augussong/VFD-Clock/Reference/IV-11引脚定义-英文版.jpg

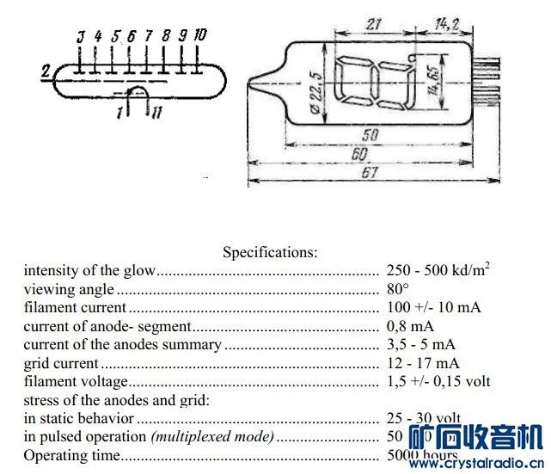
Reference/IV-11引脚定义-英文版.jpg
