augussong/VFD-Clock/Project/Software/VFD-Clock/Bsp/i2c.c

/**
  ******************************************************************************
  * @file    bsp_i2c_ee.c
  * @author  armfly 
  * @version V1.0
  * @date    2013-xx-xx
  * @brief   用gpio模拟i2c总线, 适用于STM32系列CPU。该模块不包括应用层命令帧，仅包括I2C总线基本操作函数。
  ******************************************************************************
  * @attention
  *
  * 实验平台:野火 ISO-MINI STM32 开发板 
  * 论坛    :http://www.chuxue123.com
  * 淘宝    :http://firestm32.taobao.com
  *
  ******************************************************************************
  */ 

/*
	应用说明：
	在访问I2C设备前，请先调用 i2c_CheckDevice() 检测I2C设备是否正常，该函数会配置GPIO
*/

#include "stm32f10x.h"
#include "i2c.h"

/*
*********************************************************************************************************
*	函 数 名: i2c_Delay
*	功能说明: I2C总线位延迟，最快400KHz
*	形    参：无
*	返 回 值: 无
*********************************************************************************************************
*/
void i2c_Delay(void)
{
	uint8_t i;

	/*　
	 	下面的时间是通过安富莱AX-Pro逻辑分析仪测试得到的。
		CPU主频72MHz时，在内部Flash运行, MDK工程不优化
		循环次数为10时，SCL频率 = 205KHz 
		循环次数为7时，SCL频率 = 347KHz， SCL高电平时间1.5us，SCL低电平时间2.87us 
	 	循环次数为5时，SCL频率 = 421KHz， SCL高电平时间1.25us，SCL低电平时间2.375us 
        
    IAR工程编译效率高，不能设置为7
	*/
	for (i = 0; i < 10; i++);
}

/*
*********************************************************************************************************
*	函 数 名: i2c_Start
*	功能说明: CPU发起I2C总线启动信号
*	形    参：无
*	返 回 值: 无
*********************************************************************************************************
*/
void i2c_Start(void)
{
	/* 当SCL高电平时，SDA出现一个下跳沿表示I2C总线启动信号 */
	I2C_SDA_1();
	I2C_SCL_1();
	i2c_Delay();
	I2C_SDA_0();
	i2c_Delay();
	I2C_SCL_0();
	i2c_Delay();
}

/*
*********************************************************************************************************
*	函 数 名: i2c_Start
*	功能说明: CPU发起I2C总线停止信号
*	形    参：无
*	返 回 值: 无
*********************************************************************************************************
*/
void i2c_Stop(void)
{
	/* 当SCL高电平时，SDA出现一个上跳沿表示I2C总线停止信号 */
	I2C_SDA_0();
	I2C_SCL_1();
	i2c_Delay();
	I2C_SDA_1();
	i2c_Delay();
}

/*
*********************************************************************************************************
*	函 数 名: i2c_SendByte
*	功能说明: CPU向I2C总线设备发送8bit数据
*	形    参：_ucByte ： 等待发送的字节
*	返 回 值: 无
*********************************************************************************************************
*/
void i2c_SendByte(uint8_t _ucByte)
{
	uint8_t i;

	/* 先发送字节的高位bit7 */
	for (i = 0; i < 8; i++)
	{		
		if (_ucByte & 0x80)
		{
			I2C_SDA_1();
		}
		else
		{
			I2C_SDA_0();
		}
		i2c_Delay();
		I2C_SCL_1();
		i2c_Delay();	
		I2C_SCL_0();
		if (i == 7)
		{
			 I2C_SDA_1(); // 释放总线
		}
		_ucByte <<= 1;	/* 左移一个bit */
		i2c_Delay();
	}
	i2c_Delay();
}

/*
*********************************************************************************************************
*	函 数 名: i2c_ReadByte
*	功能说明: CPU从I2C总线设备读取8bit数据
*	形    参：无
*	返 回 值: 读到的数据
*********************************************************************************************************
*/
uint8_t i2c_ReadByte(void)
{
	uint8_t i;
	uint8_t value;

	/* 读到第1个bit为数据的bit7 */
	value = 0;
	for (i = 0; i < 8; i++)
	{
		value <<= 1;
		I2C_SCL_1();
		i2c_Delay();
		if (I2C_SDA_READ())
		{
			value++;
		}
		I2C_SCL_0();
		i2c_Delay();
	}
	i2c_Delay();
	return value;
}

/*
*********************************************************************************************************
*	函 数 名: i2c_WaitAck
*	功能说明: CPU产生一个时钟，并读取器件的ACK应答信号
*	形    参：无
*	返 回 值: 返回0表示正确应答，1表示无器件响应
*********************************************************************************************************
*/
uint8_t i2c_WaitAck(void)
{
	uint8_t re;

	I2C_SDA_1();	/* CPU释放SDA总线 */
	i2c_Delay();
	I2C_SCL_1();	/* CPU驱动SCL = 1, 此时器件会返回ACK应答 */
	i2c_Delay();
	if (I2C_SDA_READ())	/* CPU读取SDA口线状态 */
	{
		re = 1;
	}
	else
	{
		re = 0;
	}
	I2C_SCL_0();
	i2c_Delay();
	return re;
}

/*
*********************************************************************************************************
*	函 数 名: i2c_Ack
*	功能说明: CPU产生一个ACK信号
*	形    参：无
*	返 回 值: 无
*********************************************************************************************************
*/
void i2c_Ack(void)
{
	I2C_SDA_0();	/* CPU驱动SDA = 0 */
	i2c_Delay();
	I2C_SCL_1();	/* CPU产生1个时钟 */
	i2c_Delay();
	I2C_SCL_0();
	i2c_Delay();
	I2C_SDA_1();	/* CPU释放SDA总线 */
	i2c_Delay();
}

/*
*********************************************************************************************************
*	函 数 名: i2c_NAck
*	功能说明: CPU产生1个NACK信号
*	形    参：无
*	返 回 值: 无
*********************************************************************************************************
*/
void i2c_NAck(void)
{
	I2C_SDA_1();	/* CPU驱动SDA = 1 */
	i2c_Delay();
	I2C_SCL_1();	/* CPU产生1个时钟 */
	i2c_Delay();
	I2C_SCL_0();
	i2c_Delay();	
}

/*
*********************************************************************************************************
*	函 数 名: IIC_WriteBytes
*	功能说明: 向指定地址写入若干数据，采用页写操作提高写入效率
*	形    参：_usAddress : 起始地址（寄存器地址）
*			 _usSize : 数据长度，单位为字节
*			 _pWriteBuf : 存放要写的数据的缓冲区指针
*			 _usDevAddr : 设备地址
*	返 回 值: 0 表示失败，1表示成功
*********************************************************************************************************
*/
uint8_t IIC_WriteBytes(uint8_t *_pWriteBuf, uint16_t _usAddress, uint16_t _usSize, uint16_t _usDevAddr)
{
	uint16_t i,m;
	uint16_t usAddr;
	

	usAddr = _usAddress;	
	for (i = 0; i < _usSize; i++)
	{
		/* 当发送第1个字节或是页面首地址时，需要重新发起启动信号和地址 */
		if (i == 0)
		{
			/*　第０步：发停止信号，启动内部写操作　*/
			i2c_Stop();
			
			/* 通过检查器件应答的方式，判断内部写操作是否完成, 一般小于 10ms 			
				CLK频率为200KHz时，查询次数为30次左右
			*/
			for (m = 0; m < 100; m++)
			{				
				/* 第1步：发起I2C总线启动信号 */
				i2c_Start();
				
				/* 第2步：发起控制字节，高7bit是地址，bit0是读写控制位，0表示写，1表示读 */
				i2c_SendByte(_usDevAddr | I2C_WR);	/* 此处是写指令 */
				
				/* 第3步：发送一个时钟，判断器件是否正确应答 */
				if (i2c_WaitAck() == 0)
				{
					break;
				}
			}
			if (m  == 1000)
			{
				goto cmd_fail;	/* 写超时 */
			}
		
			/* 第4步：发送字节地址*/
			i2c_SendByte((uint8_t)usAddr);
			
			/* 第5步：发送ACK */
			if (i2c_WaitAck() != 0)
			{
				goto cmd_fail;	/* EEPROM器件无应答 */
			}
		}
	
		/* 第6步：开始写入数据 */
		i2c_SendByte(_pWriteBuf[i]);
	
		/* 第7步：发送ACK */
		if (i2c_WaitAck() != 0)
		{
			goto cmd_fail;	/* EEPROM器件无应答 */
		}

		usAddr++;	/* 地址增1 */		
	}
	
	/* 命令执行成功，发送I2C总线停止信号 */
	i2c_Stop();
	return 1;

cmd_fail: /* 命令执行失败后，切记发送停止信号，避免影响I2C总线上其他设备 */
	/* 发送I2C总线停止信号 */
	i2c_Stop();
	return 0;
}

/*
*********************************************************************************************************
*	函 数 名: IIC_ReadBytes
*	功能说明: 从指定地址处开始读取若干数据
*	形    参：_usAddress : 起始地址（寄存器地址）
*			 _usSize : 数据长度，单位为字节
*			 _pReadBuf : 存放读到的数据的缓冲区指针
*			 _usDevAddr : 设备地址
*	返 回 值: 0 表示失败，1表示成功
*********************************************************************************************************
*/
uint8_t IIC_ReadBytes(uint8_t *_pReadBuf, uint16_t _usAddress, uint16_t _usSize, uint16_t _usDevAddr)
{
	uint16_t i;
	
	/* 第1步：发起I2C总线启动信号 */
	i2c_Start();
	
	/* 第2步：发起控制字节，高7bit是地址，bit0是读写控制位，0表示写，1表示读 */
	i2c_SendByte(_usDevAddr | I2C_WR);	/* 此处是写指令 */
	
	/* 第3步：发送ACK */
	if (i2c_WaitAck() != 0)
	{
		goto cmd_fail;	/* 器件无应答 */
	}

	/* 第4步：发送字节地址*/
	i2c_SendByte((uint8_t)_usAddress);
	
	/* 第5步：发送ACK */
	if (i2c_WaitAck() != 0)
	{
		goto cmd_fail;	/*器件无应答 */
	}
	
	/* 第6步：重新启动I2C总线。前面的代码的目的向EEPROM传送地址，下面开始读取数据 */
	i2c_Start();
	
	/* 第7步：发起控制字节，高7bit是地址，bit0是读写控制位，0表示写，1表示读 */
	i2c_SendByte(_usDevAddr | I2C_RD);	/* 此处是读指令 */
	
	/* 第8步：发送ACK */
	if (i2c_WaitAck() != 0)
	{
		goto cmd_fail;	/* 器件无应答 */
	}	
	
	/* 第9步：循环读取数据 */
	for (i = 0; i < _usSize; i++)
	{
		_pReadBuf[i] = i2c_ReadByte();	/* 读1个字节 */
		
		/* 每读完1个字节后，需要发送Ack， 最后一个字节不需要Ack，发Nack */
		if (i != _usSize - 1)
		{
			i2c_Ack();	/* 中间字节读完后，CPU产生ACK信号(驱动SDA = 0) */
		}
		else
		{
			i2c_NAck();	/* 最后1个字节读完后，CPU产生NACK信号(驱动SDA = 1) */
		}
	}
	/* 发送I2C总线停止信号 */
	i2c_Stop();
	return 1;	/* 执行成功 */

cmd_fail: /* 命令执行失败后，切记发送停止信号，避免影响I2C总线上其他设备 */
	/* 发送I2C总线停止信号 */
	i2c_Stop();
	return 0;
}

/*
*********************************************************************************************************
*	函 数 名: i2c_CfgGpio
*	功能说明: 配置I2C总线的GPIO，采用模拟IO的方式实现
*	形    参：无
*	返 回 值: 无
*********************************************************************************************************
*/
void i2c_CfgGpio(void)
{
	GPIO_InitTypeDef GPIO_InitStructure;

	RCC_APB2PeriphClockCmd(RCC_I2C_PORT, ENABLE);	/* 打开GPIO时钟 */

	GPIO_InitStructure.GPIO_Pin = I2C_SCL_PIN | I2C_SDA_PIN;
	GPIO_InitStructure.GPIO_Speed = GPIO_Speed_50MHz;
	GPIO_InitStructure.GPIO_Mode = GPIO_Mode_Out_OD;  	/* 开漏输出 */
	GPIO_Init(GPIO_PORT_I2C, &GPIO_InitStructure);

	/* 给一个停止信号, 复位I2C总线上的所有设备到待机模式 */
	i2c_Stop();
}

/*
*********************************************************************************************************
*	函 数 名: i2c_CheckDevice
*	功能说明: 检测I2C总线设备，CPU向发送设备地址，然后读取设备应答来判断该设备是否存在
*	形    参：_Address：设备的I2C总线地址
*	返 回 值: 返回值 0 表示正确， 返回1表示未探测到
*********************************************************************************************************
*/
uint8_t i2c_CheckDevice(uint8_t _Address)
{
	uint8_t ucAck;

	i2c_CfgGpio();		/* 配置GPIO */

	
	i2c_Start();		/* 发送启动信号 */

	/* 发送设备地址+读写控制bit（0 = w， 1 = r) bit7 先传 */
	i2c_SendByte(_Address | I2C_WR);
	ucAck = i2c_WaitAck();	/* 检测设备的ACK应答 */

	i2c_Stop();			/* 发送停止信号 */

	return ucAck;
}
