augussong/VFD-Clock/Project/Software/VFD-Clock/User_USB/hw_config.c

/******************** (C) COPYRIGHT 2009 STMicroelectronics ********************
* File Name          : hw_config.c
* Author             : MCD Application Team
* Version            : V3.0.1
* Date               : 04/27/2009
* Description        : Hardware Configuration & Setup
********************************************************************************
* THE PRESENT FIRMWARE WHICH IS FOR GUIDANCE ONLY AIMS AT PROVIDING CUSTOMERS
* WITH CODING INFORMATION REGARDING THEIR PRODUCTS IN ORDER FOR THEM TO SAVE TIME.
* AS A RESULT, STMICROELECTRONICS SHALL NOT BE HELD LIABLE FOR ANY DIRECT,
* INDIRECT OR CONSEQUENTIAL DAMAGES WITH RESPECT TO ANY CLAIMS ARISING FROM THE
* CONTENT OF SUCH FIRMWARE AND/OR THE USE MADE BY CUSTOMERS OF THE CODING
* INFORMATION CONTAINED HEREIN IN CONNECTION WITH THEIR PRODUCTS.
*******************************************************************************/

/* Includes ------------------------------------------------------------------*/
#include "stm32f10x_it.h"
#include "usb_lib.h"
#include "usb_prop.h"
#include "usb_desc.h"
#include "hw_config.h"
#include "platform_config.h"
#include "usb_pwr.h"

/* Private typedef -----------------------------------------------------------*/
/* Private define ------------------------------------------------------------*/
/* Private macro -------------------------------------------------------------*/
/* Private variables ---------------------------------------------------------*/

/* Extern variables ----------------------------------------------------------*/
uint8_t buffer_in[VIRTUAL_COM_PORT_DATA_SIZE];

/* Private function prototypes -----------------------------------------------*/
/* Private functions ---------------------------------------------------------*/
/*******************************************************************************
* Function Name  : Set_System
* Description    : Configures Main system clocks & power
* Input          : None.
* Return         : None.
*******************************************************************************/
void Set_System(void)
{
  GPIO_InitTypeDef GPIO_InitStructure;

  /* Setup the microcontroller system. Initialize the Embedded Flash Interface,  
     initialize the PLL and update the SystemFrequency variable. */
//  SystemInit();

  /* Enable USB_DISCONNECT GPIO clock */
  RCC_APB2PeriphClockCmd(RCC_APB2Periph_GPIO_DISCONNECT, ENABLE);

  /* Configure USB pull-up pin */
  GPIO_InitStructure.GPIO_Pin = USB_DISCONNECT_PIN;
  GPIO_InitStructure.GPIO_Speed = GPIO_Speed_50MHz;
  GPIO_InitStructure.GPIO_Mode = GPIO_Mode_Out_OD;
  GPIO_Init(USB_DISCONNECT, &GPIO_InitStructure);
}

/*******************************************************************************
* Function Name  : USB_PreInit
* Description    : Configures USB clocks, connect pin, and interrupt.
*									 本函数将初始化中用到的本文件的其他函数封装了起来
* Input          : None.
* Return         : None.
*******************************************************************************/
void USB_PreInit(void)
{
	GPIO_InitTypeDef GPIO_InitStructure;
	
	/* Enable USB_DISCONNECT GPIO clock */
  RCC_APB2PeriphClockCmd(RCC_APB2Periph_GPIO_DISCONNECT, ENABLE);

  /* Configure USB pull-up pin */
  GPIO_InitStructure.GPIO_Pin = USB_DISCONNECT_PIN;
  GPIO_InitStructure.GPIO_Speed = GPIO_Speed_50MHz;
  GPIO_InitStructure.GPIO_Mode = USB_GPIO_MODE;
  GPIO_Init(USB_DISCONNECT, &GPIO_InitStructure);
	
	// 初始化USB时钟
	Set_USBClock();
	
	//初始化USB中断（在其他地方处理）
//	USB_Interrupts_Config();
}

/*******************************************************************************
* Function Name  : Set_USBClock
* Description    : Configures USB Clock input (48MHz)
* Input          : None.
* Return         : None.
*******************************************************************************/
void Set_USBClock(void)
{
  /* USBCLK = PLLCLK / 1.5 */
  RCC_USBCLKConfig(RCC_USBCLKSource_PLLCLK_1Div5);
  /* Enable USB clock */
  RCC_APB1PeriphClockCmd(RCC_APB1Periph_USB, ENABLE);
}

/*******************************************************************************
* Function Name  : Enter_LowPowerMode
* Description    : Power-off system clocks and power while entering suspend mode
* Input          : None.
* Return         : None.
*******************************************************************************/
void Enter_LowPowerMode(void)
{
  /* Set the device state to suspend */
  bDeviceState = SUSPENDED;
}

/*******************************************************************************
* Function Name  : Leave_LowPowerMode
* Description    : Restores system clocks and power while exiting suspend mode
* Input          : None.
* Return         : None.
*******************************************************************************/
void Leave_LowPowerMode(void)
{
  DEVICE_INFO *pInfo = &Device_Info;

  /* Set the device state to the correct state */
  if (pInfo->Current_Configuration != 0)
  {
    /* Device configured */
    bDeviceState = CONFIGURED;
  }
  else
  {
    bDeviceState = ATTACHED;
  }
}

/*******************************************************************************
* Function Name  : USB_Interrupts_Config
* Description    : Configures the USB interrupts
* Input          : None.
* Return         : None.
*******************************************************************************/
void USB_Interrupts_Config(void)
{
  NVIC_InitTypeDef NVIC_InitStructure;

  NVIC_PriorityGroupConfig(NVIC_PriorityGroup_1);

  NVIC_InitStructure.NVIC_IRQChannel = USB_LP_CAN1_RX0_IRQn;
  NVIC_InitStructure.NVIC_IRQChannelPreemptionPriority = 0;
  NVIC_InitStructure.NVIC_IRQChannelSubPriority = 0;
  NVIC_InitStructure.NVIC_IRQChannelCmd = ENABLE;
  NVIC_Init(&NVIC_InitStructure);
}

/*******************************************************************************
* Function Name  : USB_Cable_Config
* Description    : Software Connection/Disconnection of USB Cable
* Input          : None.
* Return         : Status
*******************************************************************************/
void USB_Cable_Config (FunctionalState NewState)
{
  if (NewState != DISABLE)
  {
    CONNECT_CABLE();
  }
  else
  {
    DISCONNECT_CABLE();
  }
}

/*******************************************************************************
* Function Name  : Get_SerialNum.
* Description    : Create the serial number string descriptor.
* Input          : None.
* Output         : None.
* Return         : None.
*******************************************************************************/
void Get_SerialNum(void)
{
  uint32_t Device_Serial0, Device_Serial1, Device_Serial2;

  Device_Serial0 = *(__IO uint32_t*)(0x1FFFF7E8);
  Device_Serial1 = *(__IO uint32_t*)(0x1FFFF7EC);
  Device_Serial2 = *(__IO uint32_t*)(0x1FFFF7F0);

  if (Device_Serial0 != 0)
  {
    Virtual_Com_Port_StringSerial[2] = (uint8_t)(Device_Serial0 & 0x000000FF);
    Virtual_Com_Port_StringSerial[4] = (uint8_t)((Device_Serial0 & 0x0000FF00) >> 8);
    Virtual_Com_Port_StringSerial[6] = (uint8_t)((Device_Serial0 & 0x00FF0000) >> 16);
    Virtual_Com_Port_StringSerial[8] = (uint8_t)((Device_Serial0 & 0xFF000000) >> 24);

    Virtual_Com_Port_StringSerial[10] = (uint8_t)(Device_Serial1 & 0x000000FF);
    Virtual_Com_Port_StringSerial[12] = (uint8_t)((Device_Serial1 & 0x0000FF00) >> 8);
    Virtual_Com_Port_StringSerial[14] = (uint8_t)((Device_Serial1 & 0x00FF0000) >> 16);
    Virtual_Com_Port_StringSerial[16] = (uint8_t)((Device_Serial1 & 0xFF000000) >> 24);

    Virtual_Com_Port_StringSerial[18] = (uint8_t)(Device_Serial2 & 0x000000FF);
    Virtual_Com_Port_StringSerial[20] = (uint8_t)((Device_Serial2 & 0x0000FF00) >> 8);
    Virtual_Com_Port_StringSerial[22] = (uint8_t)((Device_Serial2 & 0x00FF0000) >> 16);
    Virtual_Com_Port_StringSerial[24] = (uint8_t)((Device_Serial2 & 0xFF000000) >> 24);
  }
}

/******************* (C) COPYRIGHT 2009 STMicroelectronics *****END OF FILE****/
