augussong/VFD-Clock/Project/Software/VFD-Clock/Bsp/led.h

#ifndef __LED_H
#define	__LED_H

#include "stm32f10x.h"

/** the macro definition to trigger the led on or off 
  * 1 - off
  *0 - on
  */
#define ON  0
#define OFF 1

#define RCC_LED_PORT 	RCC_APB2Periph_GPIOB
#define LEDx_PORT			GPIOB
#define LED1_PIN			GPIO_Pin_14
#define LED2_PIN			GPIO_Pin_15

/* 带参宏，可以像内联函数一样使用 */
#define LED1(a)	if (a)	\
					GPIO_SetBits(LEDx_PORT,LED1_PIN);\
					else		\
					GPIO_ResetBits(LEDx_PORT,LED1_PIN)

#define LED2(a)	if (a)	\
					GPIO_SetBits(LEDx_PORT,LED2_PIN);\
					else		\
					GPIO_ResetBits(LEDx_PORT,LED2_PIN)


/* 直接操作寄存器的方法控制IO */
#define	digitalHi(p,i)				{p->BSRR=i;}			//设置为高电平		
#define digitalLo(p,i)				{p->BRR=i;}				//输出低电平
#define digitalToggle(p,i)		{p->ODR ^=i;}			//输出反转状态


/* 定义控制IO的宏 */
#define LED1_TOGGLE()		digitalToggle(LEDx_PORT,LED1_PIN)
#define LED1_OFF()			digitalHi(LEDx_PORT,LED1_PIN)
#define LED1_ON()				digitalLo(LEDx_PORT,LED1_PIN)

#define LED2_TOGGLE()		digitalToggle(LEDx_PORT,LED2_PIN)
#define LED2_OFF()			digitalHi(LEDx_PORT,LED2_PIN)
#define LED2_ON()				digitalLo(LEDx_PORT,LED2_PIN)

void LED_Init(void);

#endif /* __LED_H */
