augussong/VFD-Clock/Project/Software/VFD-Clock/Bsp/usart2.c

/**
  ******************************************************************************
  * @file    usart2.c
  * @author  inhowe
  * @version 
  * @date    
  * @brief   
  ******************************************************************************
  * @attention
  *
  *
  ******************************************************************************
  */ 
  
#include "usart2.h"

 /**
  * @brief  USART2 GPIO 配置,工作模式配置。115200 8-N-1
  * @param  无
  * @retval 无
  */
void USART2_Init(void)
{
  GPIO_InitTypeDef GPIO_InitStructure;
  USART_InitTypeDef USART_InitStructure;
  
  /* config USART2 clock */
  RCC_APB1PeriphClockCmd(RCC_APB1Periph_USART2 | RCC_APB2Periph_GPIOA, ENABLE);
  
  /* USART2 GPIO config */
  /* Configure USART2 Tx (PA.02) as alternate function push-pull */
  GPIO_InitStructure.GPIO_Pin = GPIO_Pin_2;
  GPIO_InitStructure.GPIO_Mode = GPIO_Mode_AF_PP;
  GPIO_InitStructure.GPIO_Speed = GPIO_Speed_50MHz;
  GPIO_Init(GPIOA, &GPIO_InitStructure);

  /* Configure USART2 Rx (PA.3) as input floating */
  GPIO_InitStructure.GPIO_Pin = GPIO_Pin_3;
  GPIO_InitStructure.GPIO_Mode = GPIO_Mode_IN_FLOATING;
  GPIO_Init(GPIOA, &GPIO_InitStructure);
    
  /* USART2 mode config */
  USART_InitStructure.USART_BaudRate = 115200;
  USART_InitStructure.USART_WordLength = USART_WordLength_8b;
  USART_InitStructure.USART_StopBits = USART_StopBits_1;
  USART_InitStructure.USART_Parity = USART_Parity_No ;
  USART_InitStructure.USART_HardwareFlowControl = USART_HardwareFlowControl_None;
  USART_InitStructure.USART_Mode = USART_Mode_Rx | USART_Mode_Tx;
  USART_Init(USART2, &USART_InitStructure); 
  USART_ITConfig(USART2, USART_IT_RXNE, ENABLE);
  USART_Cmd(USART2, ENABLE);
}

u8 test[256];
u8 cnt;
void USART2_IRQHandler(void)
{
  u8 data;
  OSIntEnter();
  if(USART_GetITStatus(USART2, USART_IT_RXNE) != RESET)
  { 	
    data=USART_ReceiveData(USART2);
    test[cnt++] = data;
  }
  OSIntExit();  
}

/*********************************************END OF FILE**********************/
